philihp/Jubilee/carrot.h

uint32_t carrot[158] = {
0x00000000,
0x00000000,
0x00000000,
0x00000000,
0x00000000,
0x00000000,
0x00000000,
0x00000000,
0x00000000,
0x00030300,
0x000F0380,
0x000F03C0,
0x000F0780,
0x00078780,
0x00078780,
0x00078700,
0x0083CF04,
0x00C3CE0C,
0x00E1CE1C,
0x00F9FE3C,
0x00FDFCFC,
0x007FFFF8,
0x001FFFE0,
0x000FFFC0,
0x0007FF00,
0x0001FE00,
0x0000F800,
0x00003000,
0x00000000,
0x00000000,
0x00000000,
0x0003FE00,
0x000FFF80,
0x001FFFE0,
0x003FFFF0,
0x007FFFF0,
0x007FCFF8,
0x007E01F8,
0x00F800F8,
0x00F8007C,
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
};
